yeffrimic/BlindProject/images/circuit/13735245_1172945602727123_1960151190_n.jpg

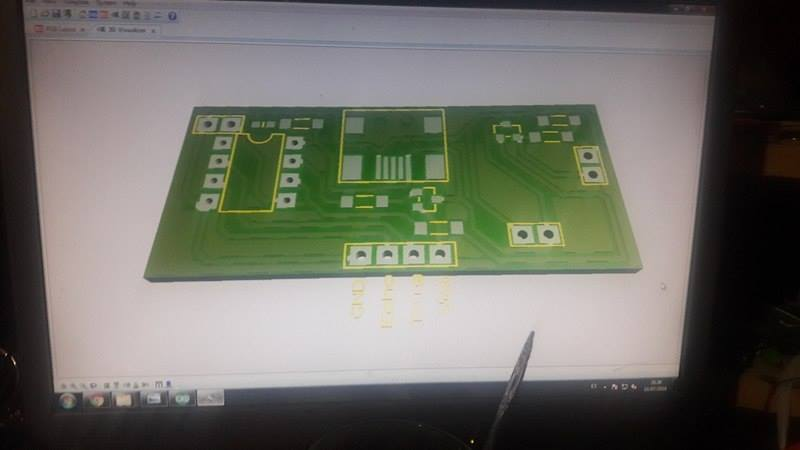
images/circuit/13735245_1172945602727123_1960151190_n.jpg
